andressantos00/MovingPets/Desenvolvimento do PCB/PCB_MAIN_2023-01-21.png

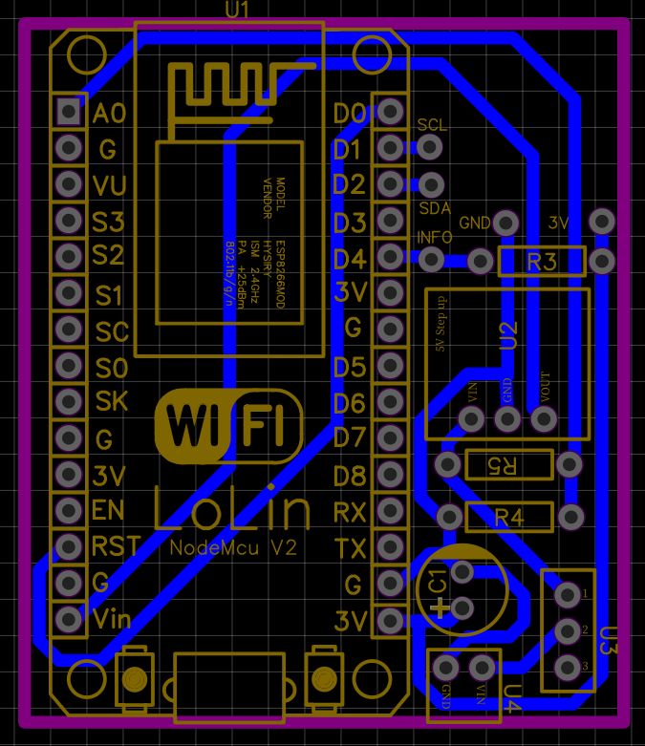
Desenvolvimento do PCB/PCB_MAIN_2023-01-21.png
