andressantos00/MovingPets/Desenvolvimento dos Modelos 3D's/Caixa Main Coleira/Box Coleira - Tampa Desenho.pdf

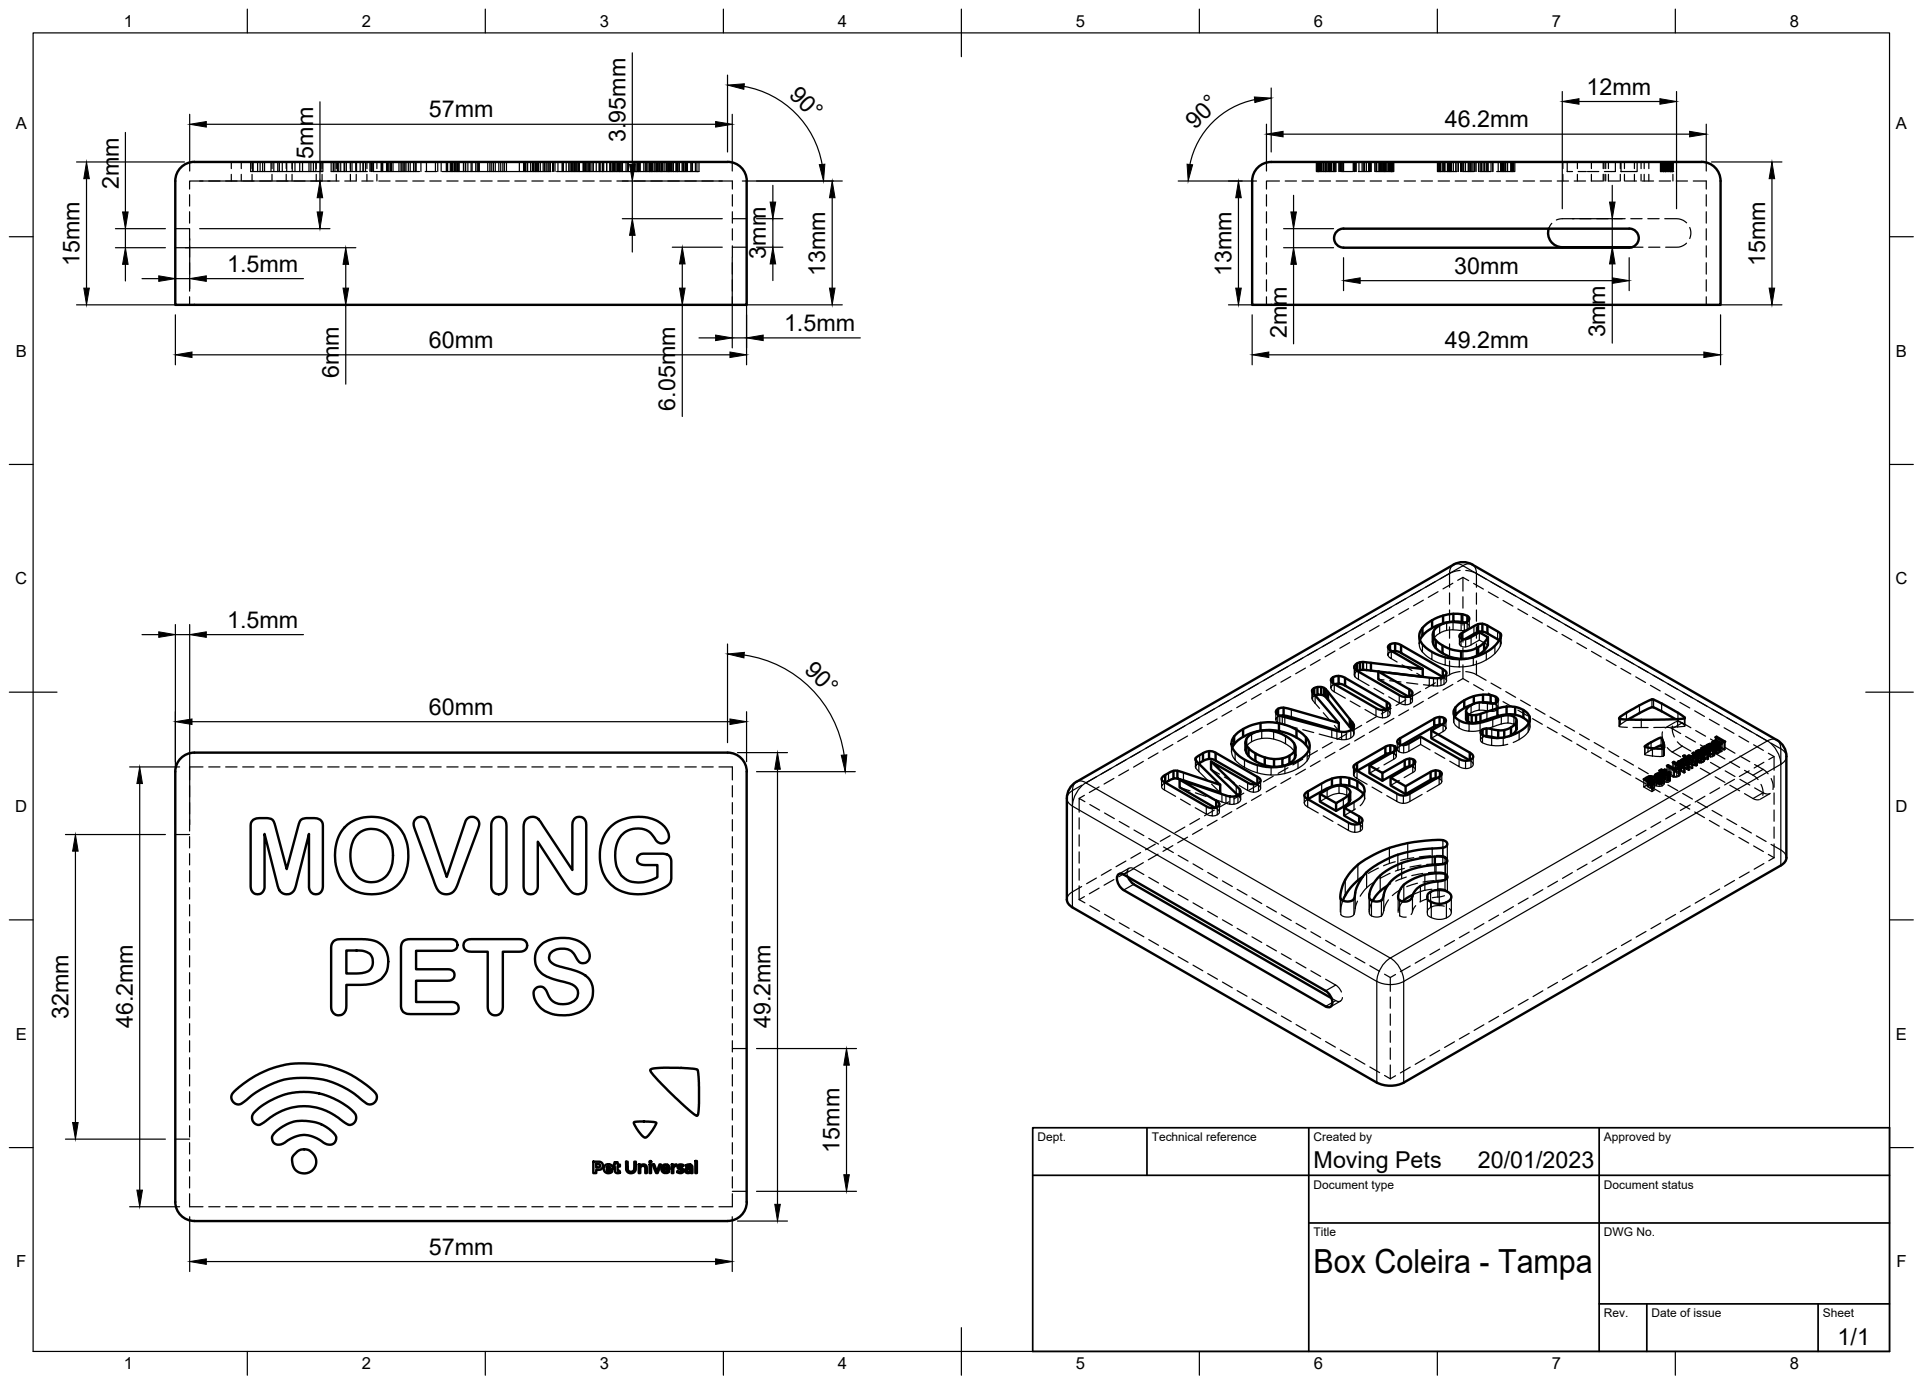
[picture p59: page 1]
Title; DWG No.; Rev.; Date of issue; Sheet; Moving Pets 13mm 3mm

Dept. | Technical reference | Created by 20/01/2023 | Approved by

Document type | Document status

Box Coleira - Tampa
