andressantos00/MovingPets/Desenvolvimento dos Modelos 3D's/Caixa Main Coleira/Box Coleira - Base Desenho.pdf

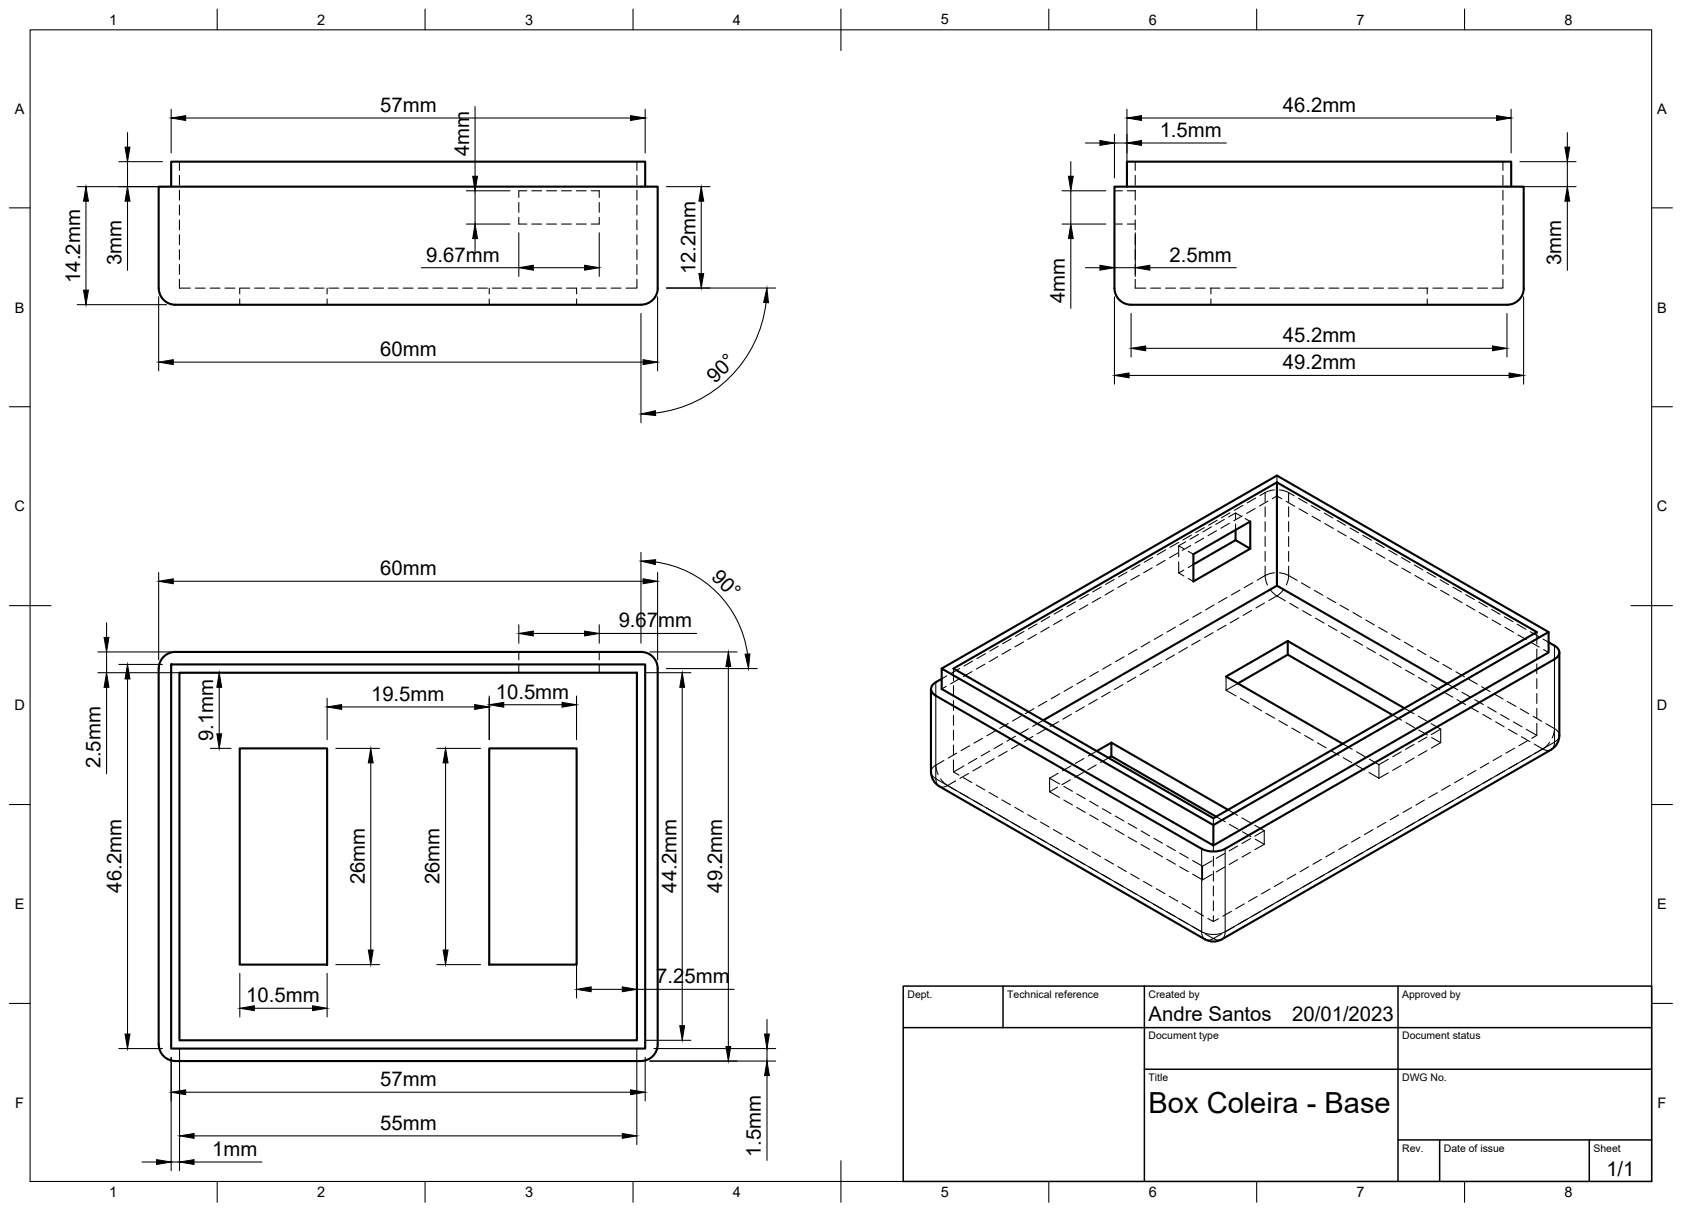
[picture p61: page 1]
Title; DWG No.; Rev.; Date of issue; Sheet

Dept. | Technical reference | Created by Andre Santos 20/01/2023 | Approved by

Document type | Document status

Box Coleira - Base
