andressantos00/MovingPets/Codigos Arduino/sensores/ESP8266_RealTime/ESP8266_RealTime.ino

#include <ESP8266WiFi.h>
#include <NTPClient.h>
#include <WiFiUdp.h>

const char *ssid     = "Vodafone-DBCD72";
const char *password = "2D7KNEEGyc93VFHF";

// Define NTP Client to get time
WiFiUDP ntpUDP;
NTPClient timeClient(ntpUDP, "pool.ntp.org");

String weekDays[7]={"Sunday", "Monday", "Tuesday", "Wednesday", "Thursday", "Friday", "Saturday"};
String months[12]={"January", "February", "March", "April", "May", "June", "July", "August", "September", "October", "November", "December"};

void setup() {
  Serial.begin(9600);
  
  Serial.print("Connecting to ");
  Serial.println(ssid);
  WiFi.begin(ssid, password);
  while (WiFi.status() != WL_CONNECTED) {
    delay(500);
    Serial.print(".");
  }
  Serial.println("Wifi connected");
  
  // Initialize a NTPClient to get time
  timeClient.begin();
  // Set offset time in seconds to adjust for your timezone, for example:
  // GMT +1 = 3600
  // GMT +8 = 28800
  // GMT -1 = -3600
  // GMT 0 = 0
  timeClient.setTimeOffset(0);
}

void loop() {
  timeClient.update();

  time_t epochTime = timeClient.getEpochTime();
  Serial.print("Epoch Time: ");
  Serial.println(epochTime);
  
  String formattedTime = timeClient.getFormattedTime();
  Serial.print("Formatted Time: ");
  Serial.println(formattedTime);  

  int currentHour = timeClient.getHours();
  Serial.print("Hour: ");
  Serial.println(currentHour);  

  int currentMinute = timeClient.getMinutes();
  Serial.print("Minutes: ");
  Serial.println(currentMinute); 
   
  int currentSecond = timeClient.getSeconds();
  Serial.print("Seconds: ");
  Serial.println(currentSecond);  

  String weekDay = weekDays[timeClient.getDay()];
  Serial.print("Week Day: ");
  Serial.println(weekDay);    

  //Get a time structure
  struct tm *ptm = gmtime ((time_t *)&epochTime); 

  int monthDay = ptm->tm_mday;
  Serial.print("Month day: ");
  Serial.println(monthDay);

  int currentMonth = ptm->tm_mon+1;
  Serial.print("Month: ");
  Serial.println(currentMonth);

  String currentMonthName = months[currentMonth-1];
  Serial.print("Month name: ");
  Serial.println(currentMonthName);

  int currentYear = ptm->tm_year+1900;
  Serial.print("Year: ");
  Serial.println(currentYear);

  //Print complete date:
  String currentDate = String(currentYear) + "-" + String(currentMonth) + "-" + String(monthDay);
  Serial.print("Current date: ");
  Serial.println(currentDate);

  Serial.println("");

  delay(2000);
}
